Rhetticle/HVDC/Simulations/HVDC.asc

C1: cap; 10m
C2: cap; 0.66µ
D3: schottky
L1: ind2; 26µ; Rser=0.2
L2: ind2; 453m; Rser=1500
L3: ind2; 26µ; Rser=0.2
L4: ind2; 453m; Rser=1500
M1: nmos; IPI200N25N3
M2: nmos; IPI200N25N3
M3: nmos; IPI200N25N3
M4: nmos; IPI200N25N3
R1: res; 100
R2: res; 10k
R3: res; 10000000
R4: res; 100
R5: res; 10k
R6: res; 10k
R7: res; 100
R8: res; 10k
R9: res; 100
S1: sw
V1: voltage; 7.4
V2: voltage; PULSE(0 12 0 1n 1n 25u 50u)
V3: voltage; PULSE(0 12 10ms 1n 1n 100ms 200ms 1)
V4: voltage; PULSE(0 12 0 1n 1n 25u 50u)
V5: voltage; PULSE(0 12 25u 1n 1n 25u 50u)
V6: voltage; PULSE(0 12 25u 1n 1n 25u 50u)
Named nets: 0
.tran 12ms
K L1 L2 0.8
K1 L3 L4 1
